VultureWood/KettlebellCounter/Mechanics/CAD-files/Frame_3D_printed/Frame_for_Kettlebell_Counter_Primcipal_assembly_2.png

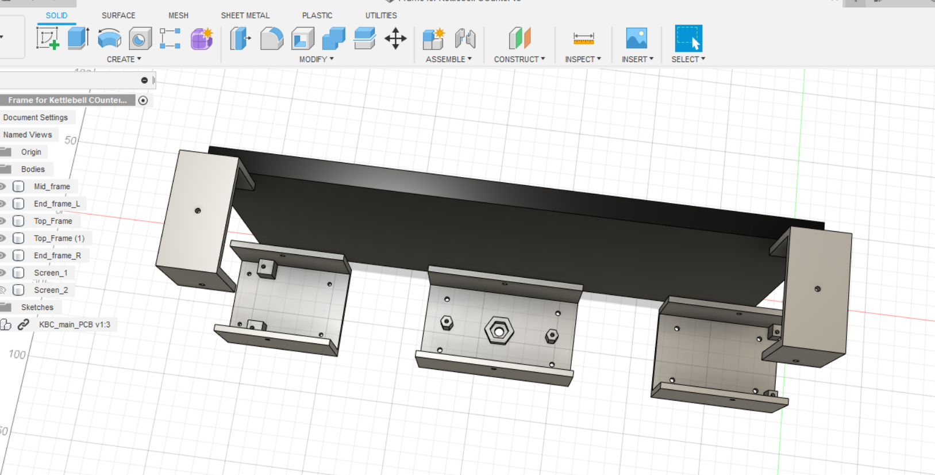
Mechanics/CAD-files/Frame_3D_printed/Frame_for_Kettlebell_Counter_Primcipal_assembly_2.png
