VultureWood/KettlebellCounter/Mechanics/CAD-files/Frame_3D_printed/Insta_pic_3.png

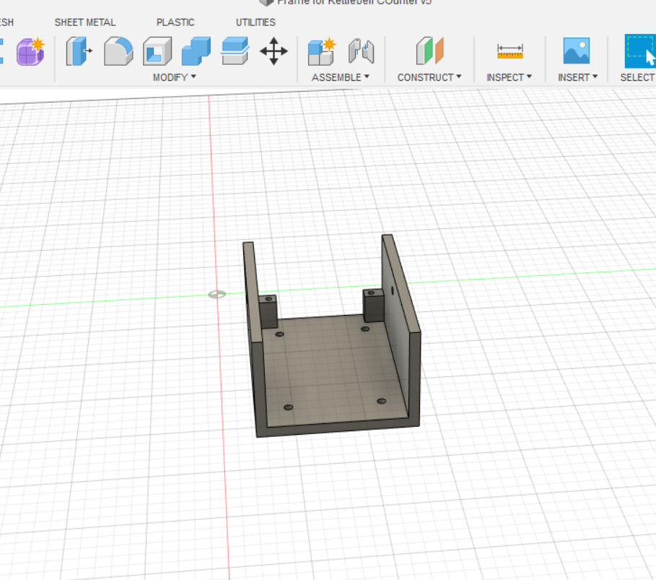
Mechanics/CAD-files/Frame_3D_printed/Insta_pic_3.png
